JohnArild/CANtest/STM32CAN/Inc/BSP.h

/**
  ******************************************************************************
  * @file    BSP.h
  * @author  John Arild Lolland
  ******************************************************************************
*/

#ifndef BSP_H_
#define BSP_H_

#include "stm32f042x6.h"

class BSP_STM32CAN {
    public:
        int initilize();
    private:
        int MCUspeed_48MHz();
        int setup_GPIO();
        int setup_CAN();
        int setup_SPI();
};

#endif /* BSP_H_ */
